td0g/ballistic_chronograph_mk2/Firmware/clockCal/1.0/clockCal/clockCal.ino

/*
  Firmware for measuring Arduino clock speed
  Written by Tyler Gerritsen
  vtgerritsen@gmail.com
  www.td0g.ca

DESCRIPTION:
  Simple way to measure the actual speed of an Arduino Uno
  A stopwatch is required.  Start the stopwatch simultaneously with the Arduino by sending a serial character.
  Adjust the Arduino's clock speed by entering 't99.8' to slow the clock by 0.2%
  After a couple minutes, the clock can be calibrated very accurately!

CHANGELOG:
  1.0
    2020-07-26
    Initial Release

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
  You should have received a copy of the GNU General Public License
  along with this program.  If not, see <https://www.gnu.org/licenses/>.
 */







//SETUP ####################################################################################
//Definitions - PLEASE SET UP BEFORE USING

//Serial port baud rate
#define BAUD 9600

//END OF SETUP ##############################################################################


//Serial
  char serialBuffer[20];
  int sofar = 0;
  float _timeFactor = 1.0;
  unsigned long _time = 1000;
  unsigned long _adjustedTime = 1000;
  unsigned long _startTime;




void setup() {
//Start communicating with PC
  Serial.begin(BAUD);   
  Serial.println(F("Prepare a stopwatch"));  //Hello world message
  Serial.println(F("When you are ready, send a character over Serial"));
  Serial.println(F("Then the Arduino will count down until it begins its count"));
  Serial.println(F("Start the stopwatch when the count down reaches 0"));
  Serial.println(F("After some time, you may adjust the clock rate by entering a %"));
  Serial.println(F("For instance: enter 't99.8' to slow down the clock by 0.2%"));
  delay(100);
  while (!Serial.available()){};
  while (Serial.available()) Serial.read();
  _adjustedTime = millis() + 1000;
  Serial.print("STARTING in 3...");
  while (millis() < _adjustedTime){};
  Serial.print(" 2...");
  _adjustedTime += 1000;
  while (millis() < _adjustedTime){};
  Serial.print(" 1...");
  _adjustedTime += 1000;
  while (millis() < _adjustedTime){};
  Serial.println(" NOW");
  _time = 0;
  _startTime = millis();
}


void loop(){
//Print clock
  if (millis() > _adjustedTime){
    Serial.print(_time / 1000);
    Serial.print(F(".0 s      "));
    delay(400);
    Serial.print(F("50ms error = +/- "));
    Serial.print(5000.0 / _time,4);
    Serial.println(F("%"));
    _time += 1000;
    _adjustedTime = _time / _timeFactor + _startTime;
  }
//Read serial
  if (Serial.available()){
    char _c = Serial.read();
    if (_c == 10 || _c == 13){  //Newline character

    //Read new timefactor
      if (serialBuffer[0] != 't'){
        Serial.println(F("   ERROR - Please enter factor starting with 't'"));
        Serial.println(F("   eg. 't100.2'"));
        Serial.println();
        Serial.print(F("Current Time Factor: "));
        Serial.println(_timeFactor,4);
        Serial.print(F("Clock Speed: "));
        Serial.print(_timeFactor * 16,4);
      }
      else{
        serialBuffer[sofar] = 0;
        _timeFactor = parseNumber('t',_timeFactor * 100) / 100;
        Serial.print(F("New Time Factor: "));
        Serial.println(_timeFactor,4);
        Serial.print(F("Clock Speed: "));
        Serial.print(_timeFactor * 16,4);
        Serial.println(F(" MHz"));
  
      //Adjust clock
        _adjustedTime = _time / _timeFactor;
        while (_adjustedTime > millis()){
          _time -= 1000;
        _adjustedTime = _time / _timeFactor + _startTime;
        }
        while (_adjustedTime < millis()){
          _time += 1000;
        _adjustedTime = _time / _timeFactor + _startTime;
        }
      }
        sofar = 0;
    }

  //Read serial into buffer
    else {
      serialBuffer[sofar] = _c;
      sofar++;
    }
  }
}



float parseNumber(char code,float val) {
  char *ptr=serialBuffer;  // start at the beginning of buffer
  while((long)ptr > 1 && (*ptr) && (long)ptr < (long)serialBuffer+sofar) {  // walk to the end
    if(*ptr==code) {  // if you find code on your walk,
      return atof(ptr+1);  // convert the digits that follow into a float and return it
    }
    ptr++;  // take a step from here to the letter after the next space
  }
  return val;  // end reached, nothing found, return default val.
}
